shadowjohn/helmet_rpm_led/snapshot/s1.png

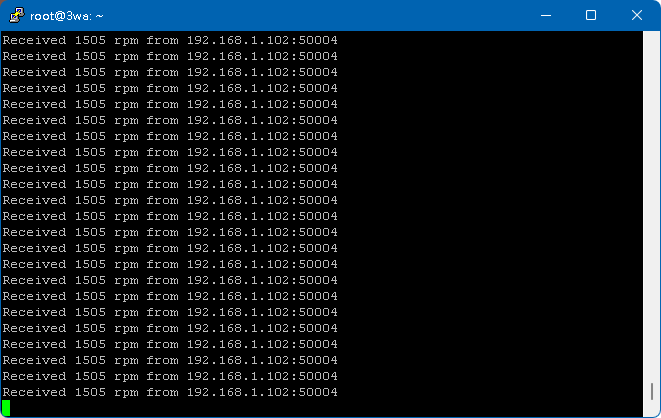
snapshot/s1.png
